morganvenable/lalboard/kicad_svalboard/datasheets/LIB_FH34SRJ-8S-0.5SH_50_/FH34SRJ-8S-0.5SH_50_/KiCad/main_board_FFC.kicad_sch

## KiCad design kicad_svalboard/datasheets/LIB_FH34SRJ-8S-0.5SH_50_/FH34SRJ-8S-0.5SH_50_/KiCad/main_board_FFC.kicad_sch (2022-11-17)

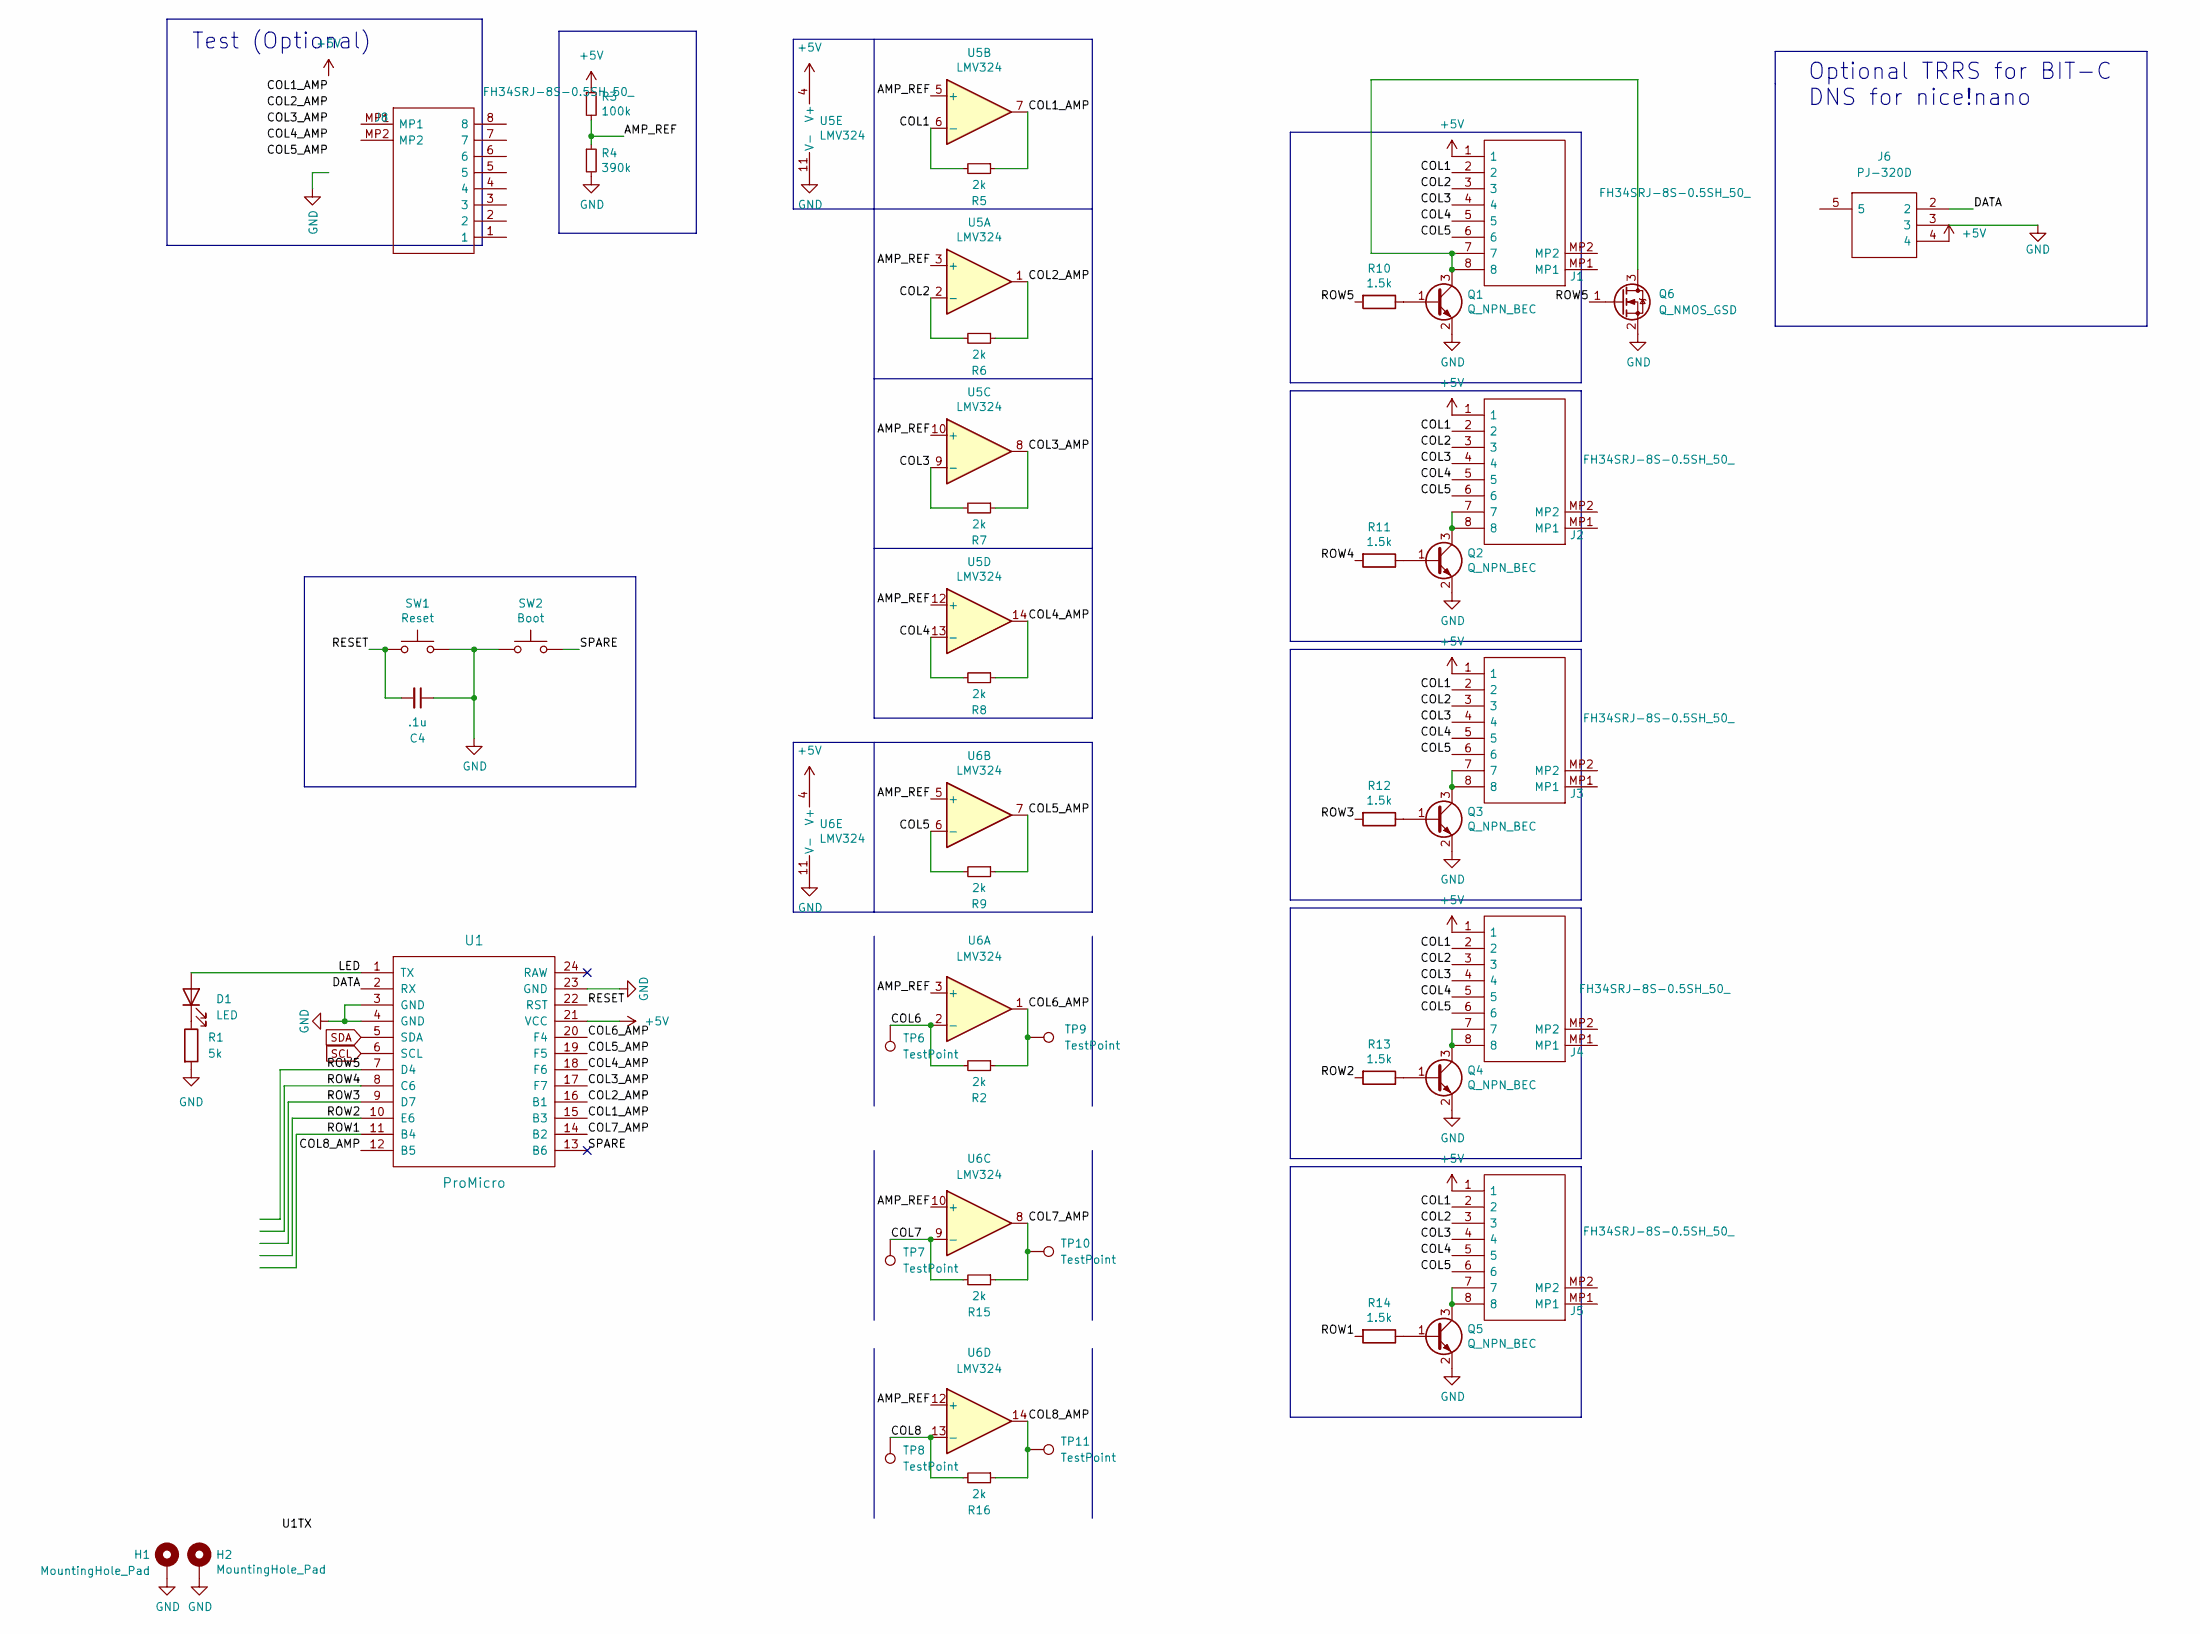
[picture p17: schematic main_board_FFC.kicad_sch]

Parts:
C4: .1u; C_0805_2012Metric_Pad1.15x1.40mm_HandSolder; Voltage 16V; Tolerance 10%
D1: LED; LED_0805_2012Metric_Pad1.15x1.40mm_HandSolder
H1, H2: MountingHole_Pad; MountingHole_3.2mm_M3_DIN965_Pad
J1, J2, J3, J4, J5, J8: FH34SRJ-8S-0.5SH_50_; FH34SRJ8S05SH50; Manufacturer_Part_Number FH34SRJ-8S-0.5SH(50); Mouser Part Number 798-FH34SRJ8S05SH50
J6: PJ-320D; Manufacturer_Part_Number PJ-320D
Q1, Q2, Q3, Q4, Q5: Q_NPN_BEC; SOT-23_Handsoldering; Part PMBT2222A,215
Q6: Q_NMOS_GSD; SOT-23_Handsoldering
R1: 5k; R_0805_2012Metric_Pad1.20x1.40mm_HandSolder
R2, R15, R16: 2k; R_0805_2012Metric_Pad1.20x1.40mm_HandSolder
R3: 100k; R_0805_2012Metric_Pad1.15x1.40mm_HandSolder
R4: 390k; R_0805_2012Metric_Pad1.15x1.40mm_HandSolder
R5, R6, R7, R8, R9: 2k; R_0805_2012Metric_Pad1.15x1.40mm_HandSolder
R10, R11, R12, R13, R14: 1.5k; R_0805_2012Metric_Pad1.15x1.40mm_HandSolder
SW1: Reset; SW_PUSH_6mm_H5mm; Part 1825910-6
SW2: Boot; SW_PUSH_6mm_H5mm; Part 1825910-6
TP6, TP7, TP8, TP9, TP10, TP11: TestPoint; TestPoint_THTPad_D1.0mm_Drill0.5mm
U1: ProMicro; ProMicro_v3.5
U5, U6: LMV324; TSSOP-14_4.4x5mm_P0.65mm

Connections:
+5V: J1.1, J2.1, J3.1, J4.1, J5.1, J6.4, R3.1, U1.21 (VCC), U5.4 (V+), U6.4 (V+)
AMP_REF: R3.2, R4.1, U5.3 (+), U5.5 (+), U5.10 (+), U5.12 (+), U6.3 (+), U6.5 (+), U6.10 (+), U6.12 (+)
COL1: J1.2, J2.2, J3.2, J4.2, J5.2, R5.2, U5.6 (-)
COL1_AMP: R5.1, U1.15 (B3), U5.7
COL2: J1.3, J2.3, J3.3, J4.3, J5.3, R6.2, U5.2 (-)
COL2_AMP: R6.1, U1.16 (B1), U5.1
COL3: J1.4, J2.4, J3.4, J4.4, J5.4, R7.2, U5.9 (-)
COL3_AMP: R7.1, U1.17 (F7), U5.8
COL4: J1.5, J2.5, J3.5, J4.5, J5.5, R8.2, U5.13 (-)
COL4_AMP: R8.1, U1.18 (F6), U5.14
COL5: J1.6, J2.6, J3.6, J4.6, J5.6, R9.2, U6.6 (-)
COL5_AMP: R9.1, U1.19 (F5), U6.7
COL6: R2.2, TP6.1, U6.2 (-)
COL6_AMP: R2.1, TP9.1, U1.20 (F4), U6.1
COL7: R15.2, TP7.1, U6.9 (-)
COL7_AMP: R15.1, TP10.1, U1.14 (B2), U6.8
COL8: R16.2, TP8.1, U6.13 (-)
COL8_AMP: R16.1, TP11.1, U1.12 (B5), U6.14
DATA: J6.2, U1.2 (RX)
GND: C4.1, H1.1, H2.1, J6.3, Q1.2 (E), Q2.2 (E), Q3.2 (E), Q4.2 (E), Q5.2 (E), Q6.2 (S), R1.2, R4.2, SW1.2, SW2.2, U1.3 (GND), U1.4 (GND), U1.23 (GND), U5.11 (V-), U6.11 (V-)
LED: D1.2 (A), U1.1 (TX)
unnamed: D1.1 (K), R1.1
unnamed: J1.7, J1.8, Q1.3 (C), Q6.3 (D)
unnamed: J2.7, J2.8, Q2.3 (C)
unnamed: J3.7, J3.8, Q3.3 (C)
unnamed: J4.7, J4.8, Q4.3 (C)
unnamed: J5.7, J5.8, Q5.3 (C)
unnamed: Q1.1 (B), R10.1
unnamed: Q2.1 (B), R11.1
unnamed: Q3.1 (B), R12.1
unnamed: Q4.1 (B), R13.1
unnamed: Q5.1 (B), R14.1
RESET: C4.2, SW1.1, U1.22 (RST)
ROW1: R14.2, U1.11 (B4)
ROW2: R13.2, U1.10 (E6)
ROW3: R12.2, U1.9 (D7)
ROW4: R11.2, U1.8 (C6)
ROW5: Q6.1 (G), R10.2, U1.7 (D4)
SCL: U1.6 (SCL)
SDA: U1.5 (SDA)
SPARE: SW2.1, U1.13 (B6)

Notes on the sheet:
Test (Optional)
Optional TRRS for BIT-C DNS for nice!nano
